lukasznowarkiewicz/ApplianceConnector/imagesAndVideos/api_sample.png

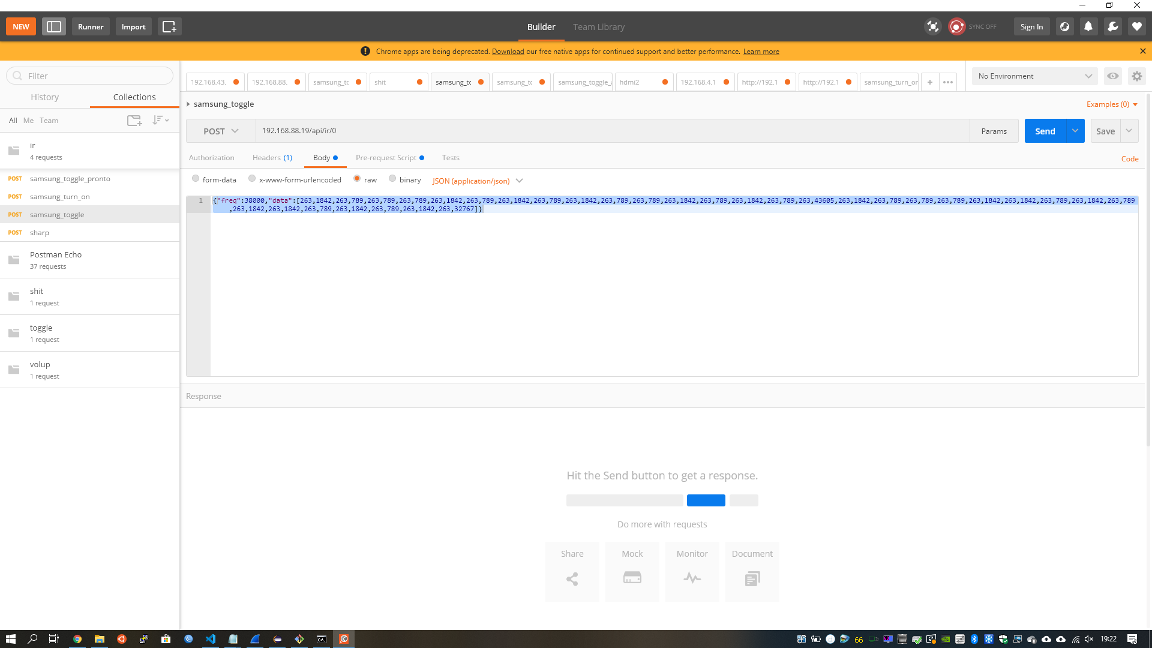
imagesAndVideos/api_sample.png
