lukasznowarkiewicz/ApplianceConnector/imagesAndVideos/box2.png

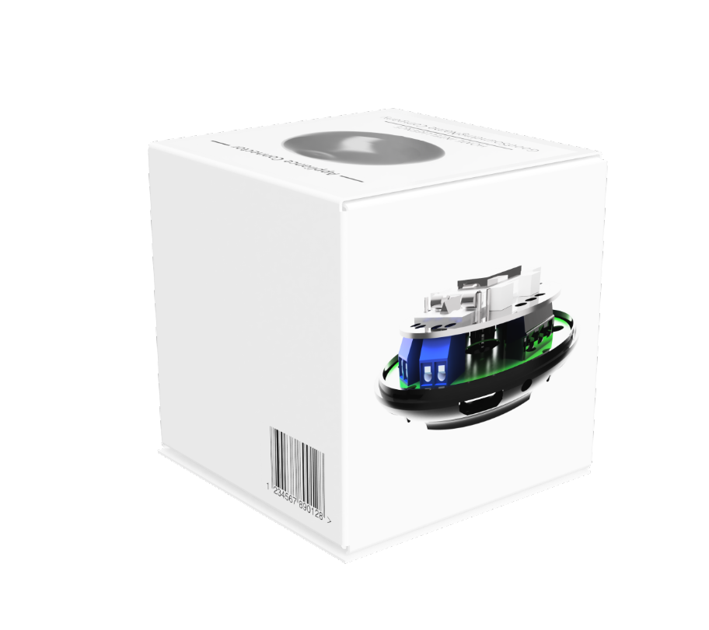
imagesAndVideos/box2.png
