lukasznowarkiewicz/ApplianceConnector/imagesAndVideos/box.png

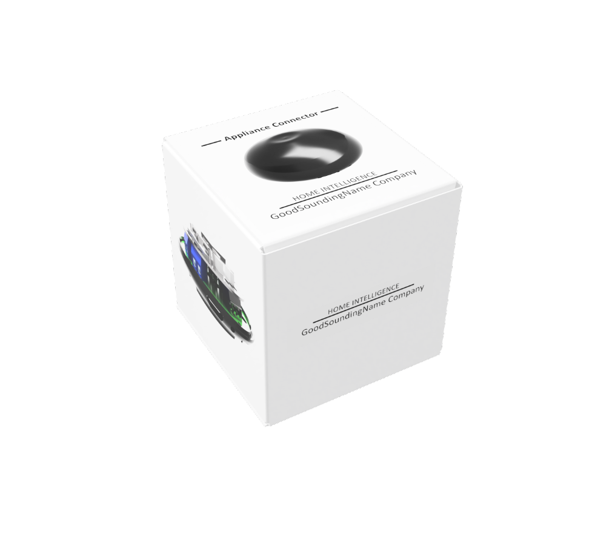
imagesAndVideos/box.png
