lukasznowarkiewicz/ApplianceConnector/imagesAndVideos/casing/casing_bottom_view.jpeg

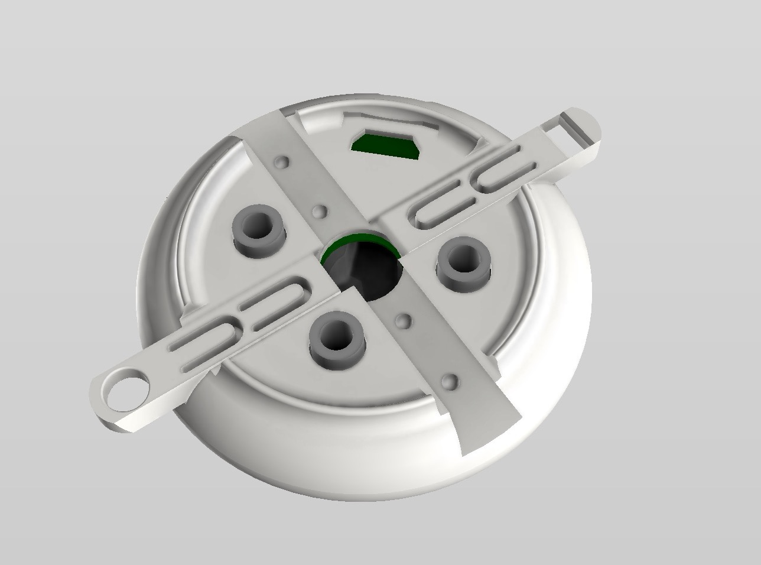
imagesAndVideos/casing/casing_bottom_view.jpeg
