lukasznowarkiewicz/ApplianceConnector/imagesAndVideos/casing/casing_render.jpg

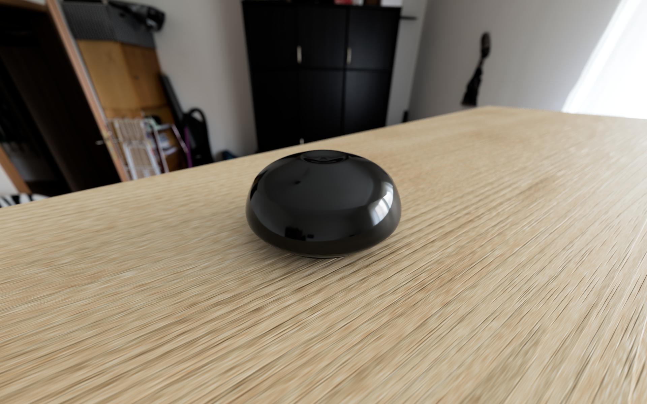
imagesAndVideos/casing/casing_render.jpg
