lukasznowarkiewicz/ApplianceConnector/imagesAndVideos/devKit_prepapration.jpeg

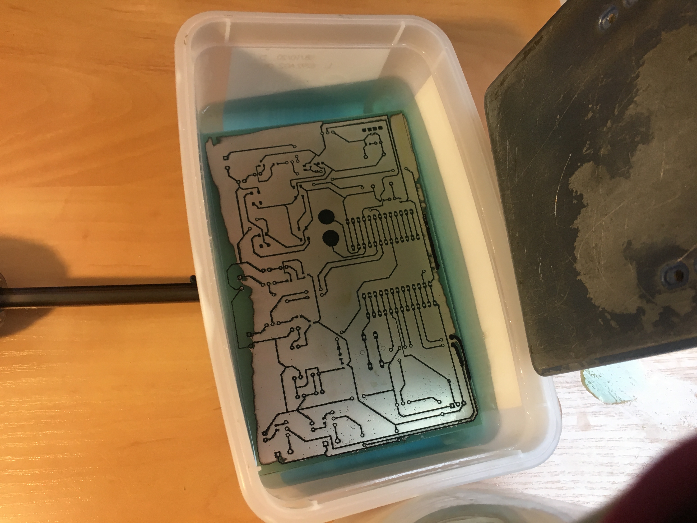
imagesAndVideos/devKit_prepapration.jpeg
