lukasznowarkiewicz/ApplianceConnector/imagesAndVideos/software/authentication.png

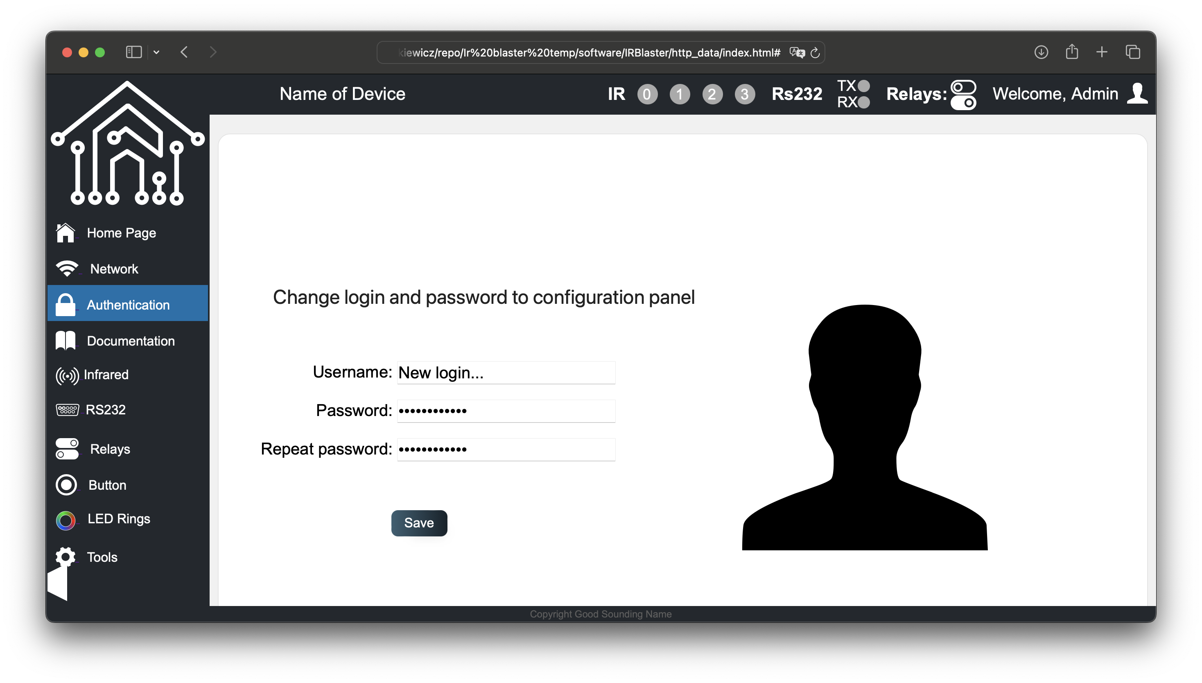
imagesAndVideos/software/authentication.png
