lukasznowarkiewicz/ApplianceConnector/imagesAndVideos/software/button1.png

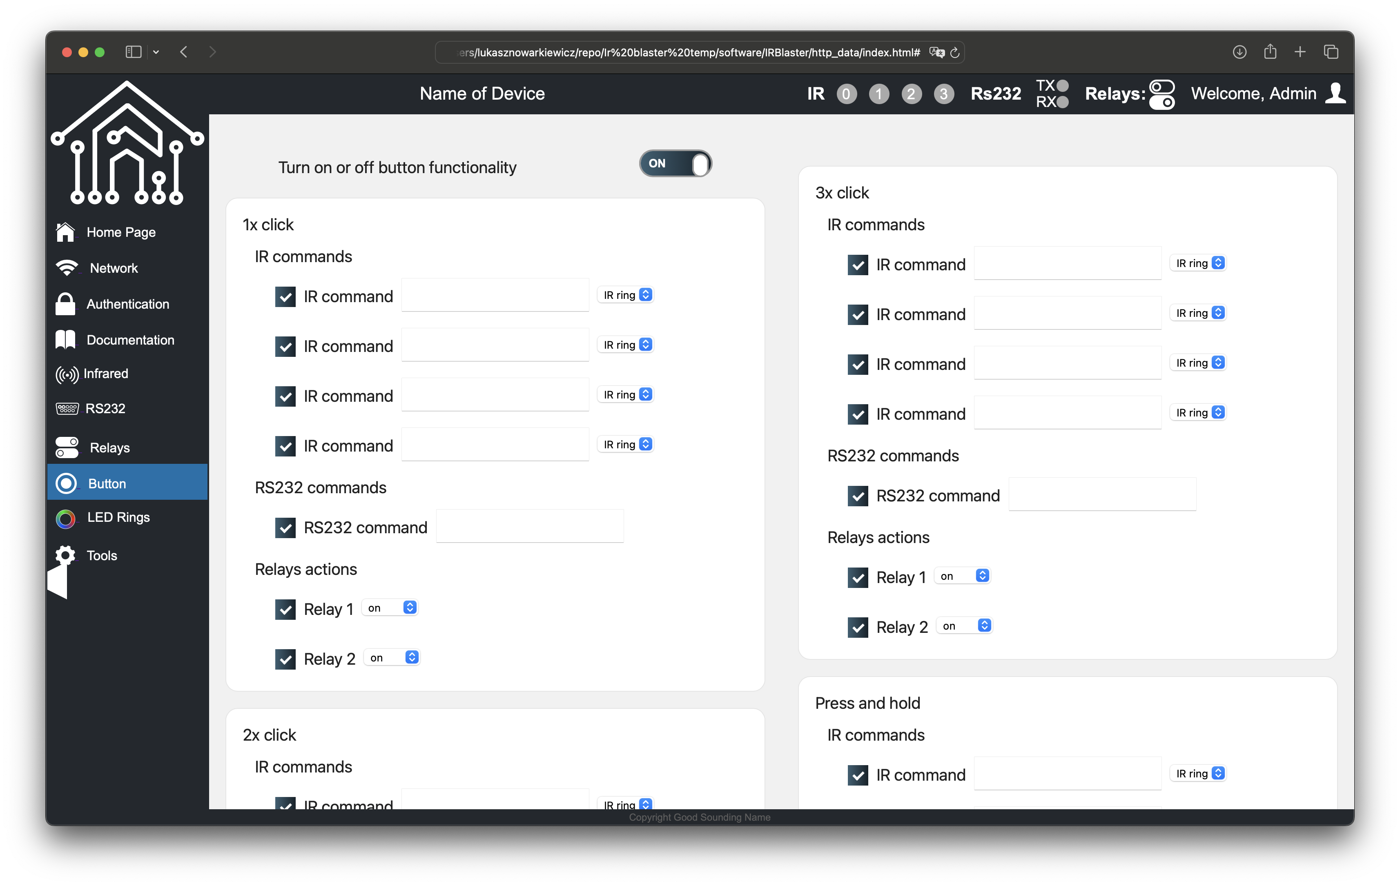
imagesAndVideos/software/button1.png
