lukasznowarkiewicz/ApplianceConnector/imagesAndVideos/software/button2.png

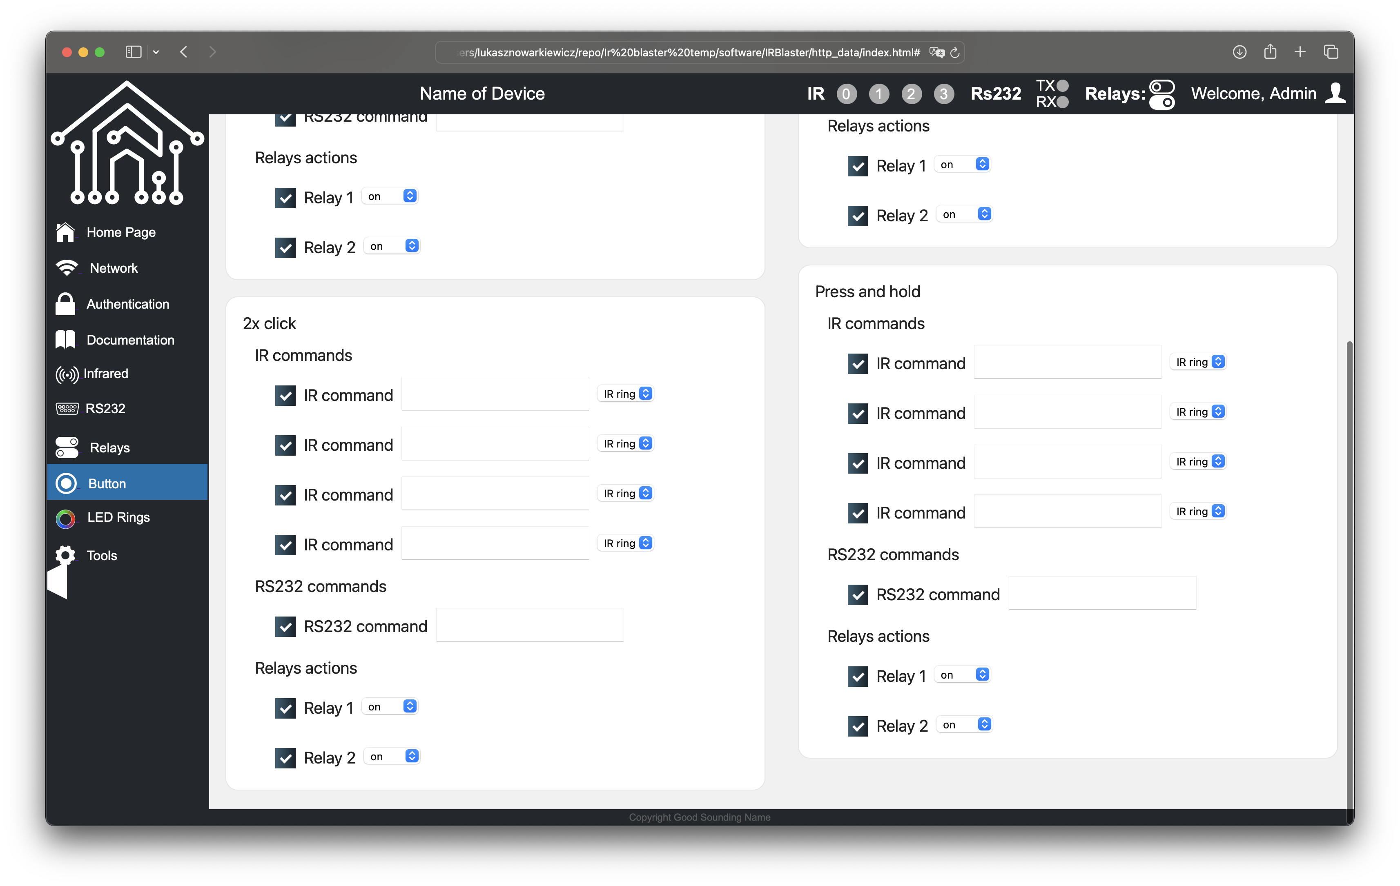
imagesAndVideos/software/button2.png
