lukasznowarkiewicz/ApplianceConnector/imagesAndVideos/software/documentation.png

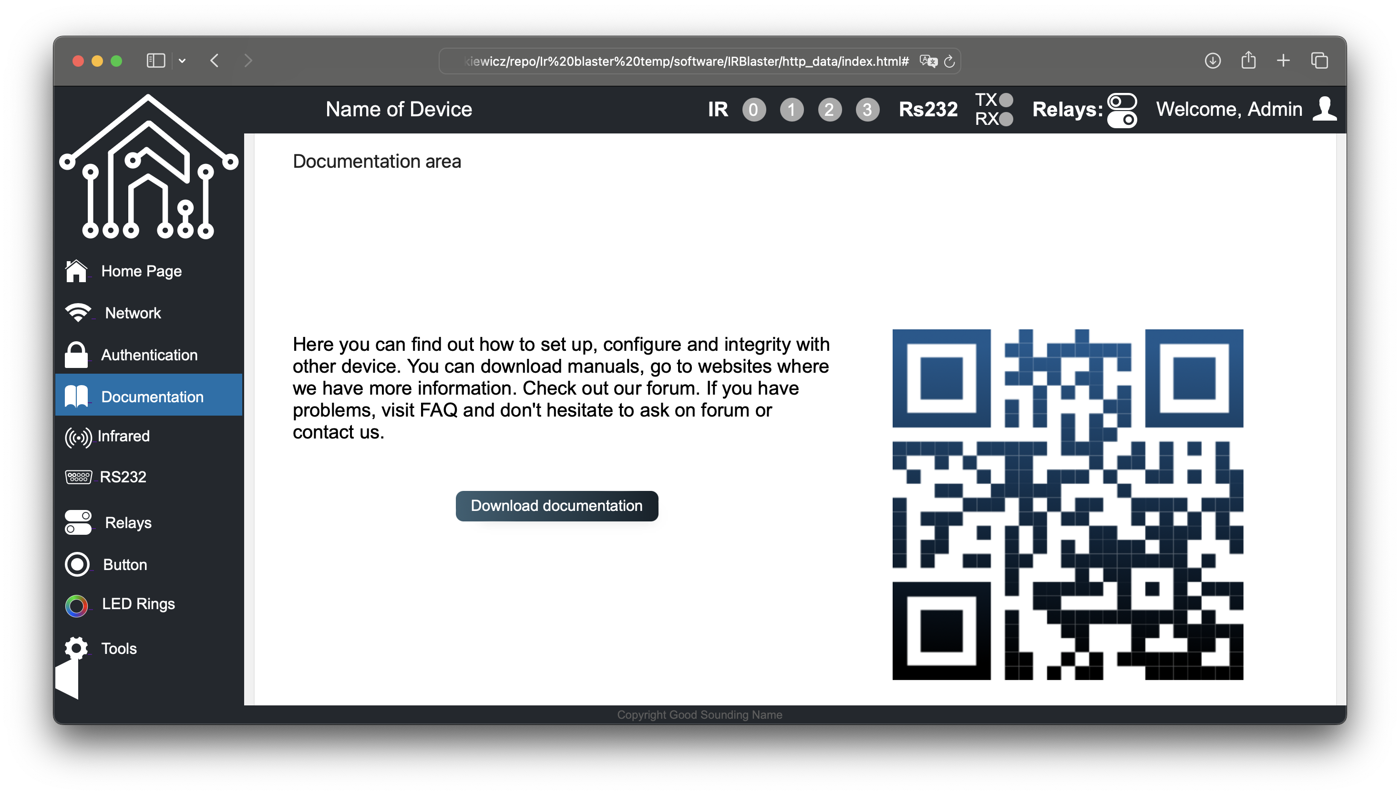
imagesAndVideos/software/documentation.png
