lukasznowarkiewicz/ApplianceConnector/imagesAndVideos/software/homePages.png

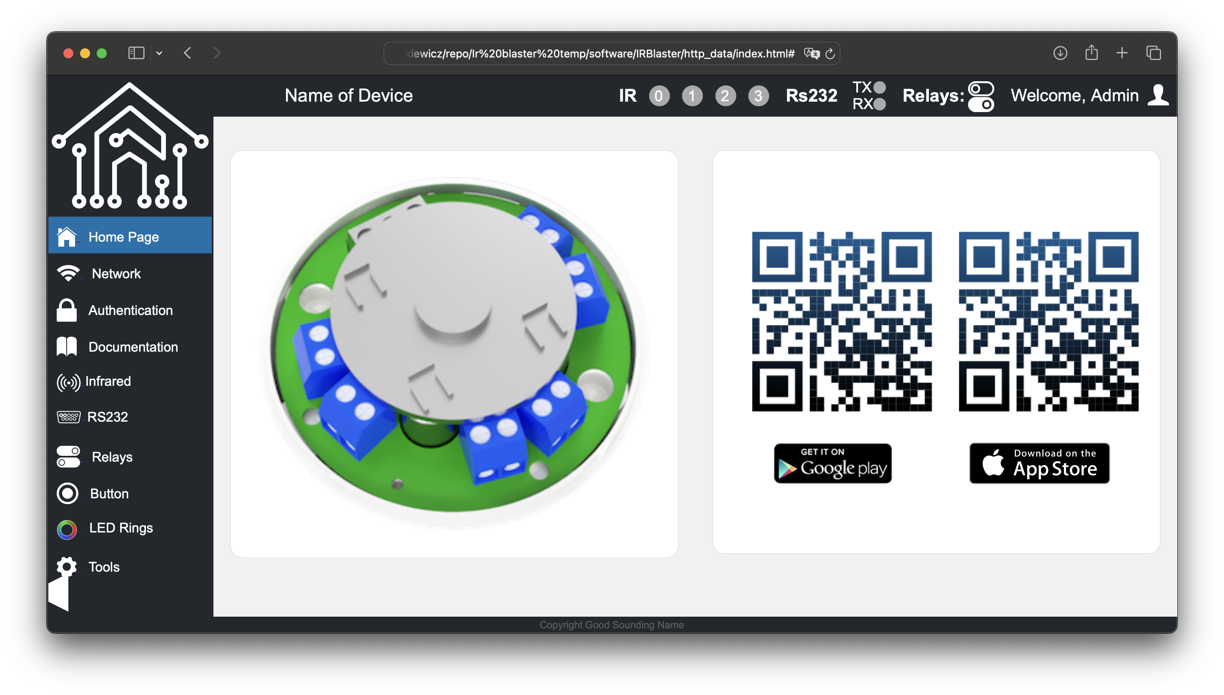
imagesAndVideos/software/homePages.png
