lukasznowarkiewicz/ApplianceConnector/imagesAndVideos/software/infrared.png

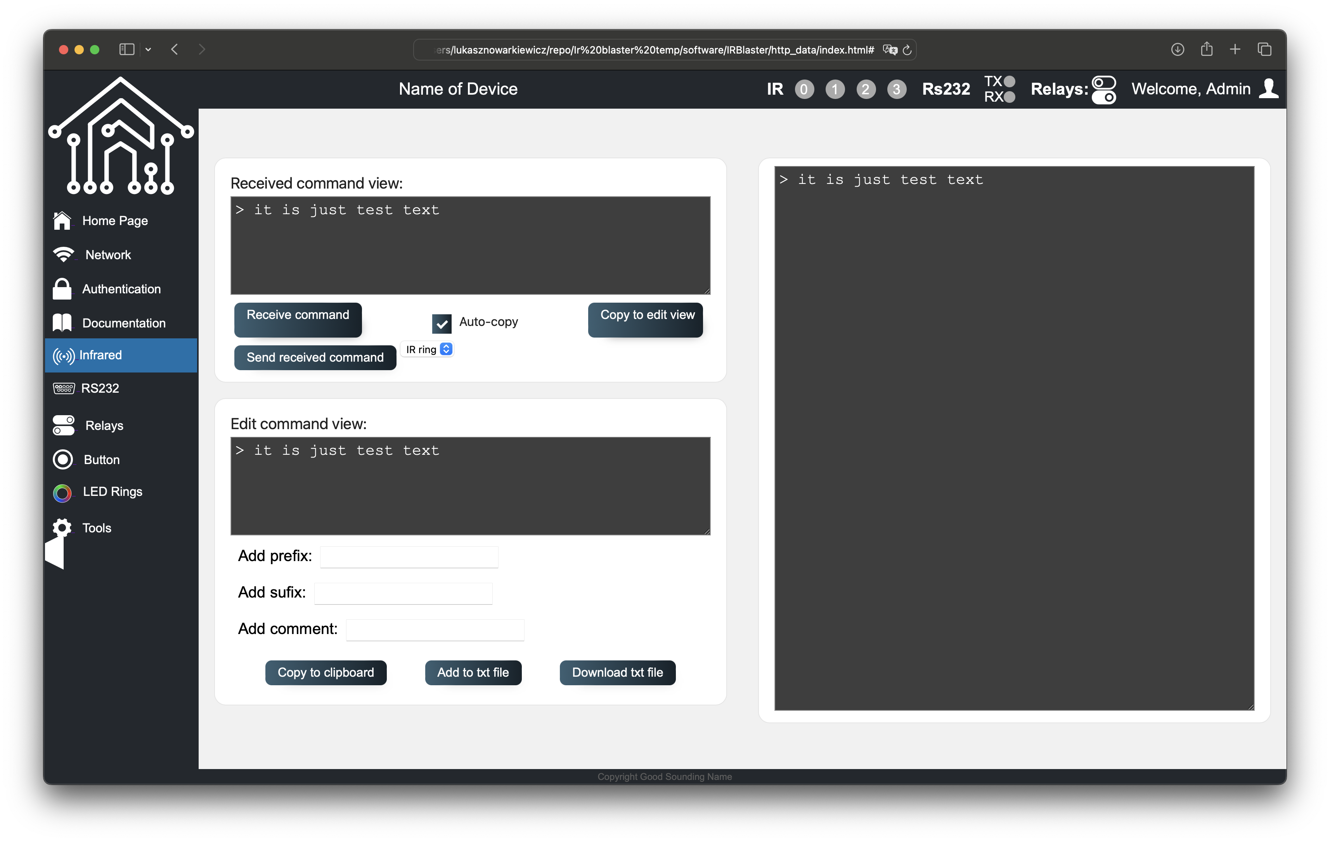
imagesAndVideos/software/infrared.png
