lukasznowarkiewicz/ApplianceConnector/imagesAndVideos/software/ledRing.png

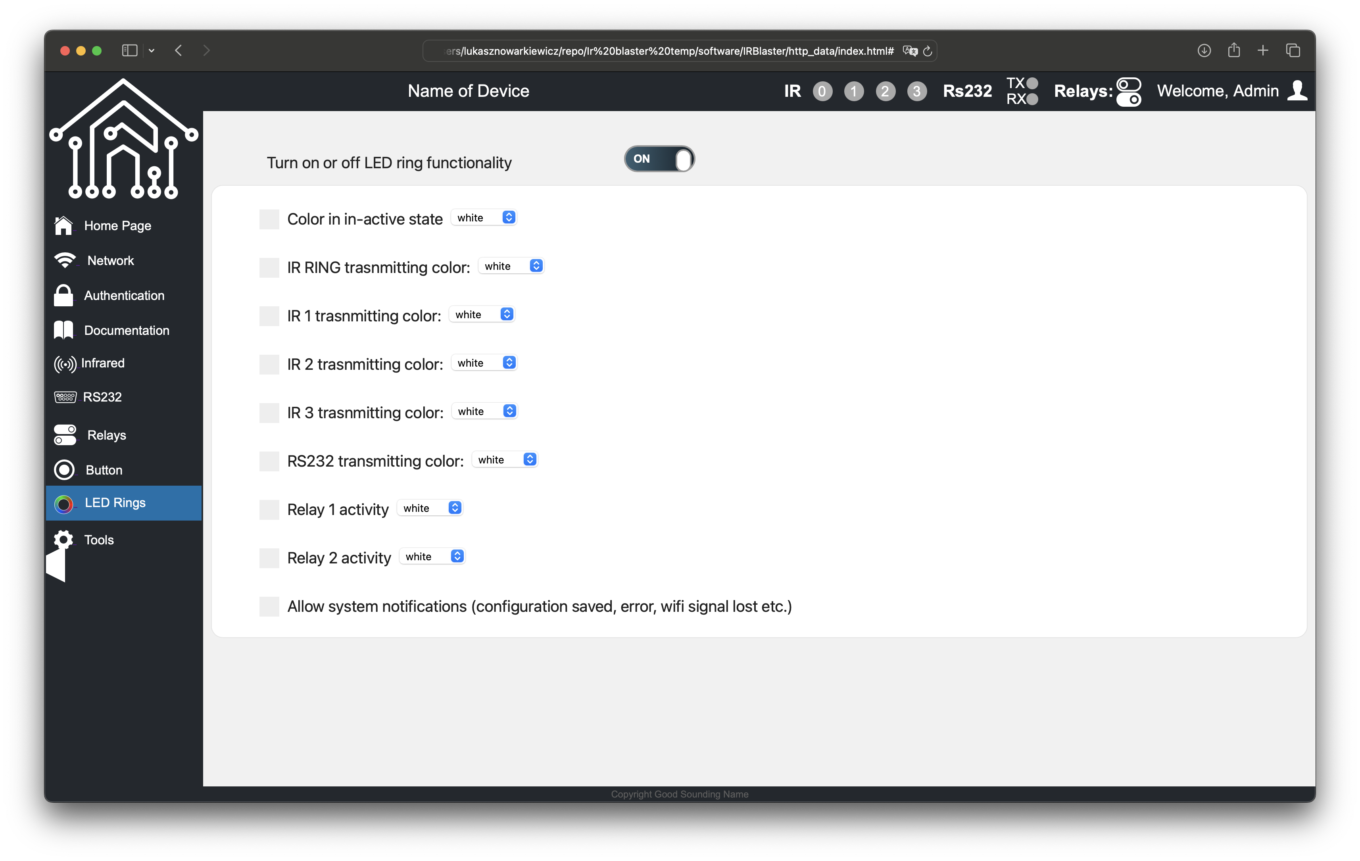
imagesAndVideos/software/ledRing.png
