lukasznowarkiewicz/ApplianceConnector/imagesAndVideos/software/network.png

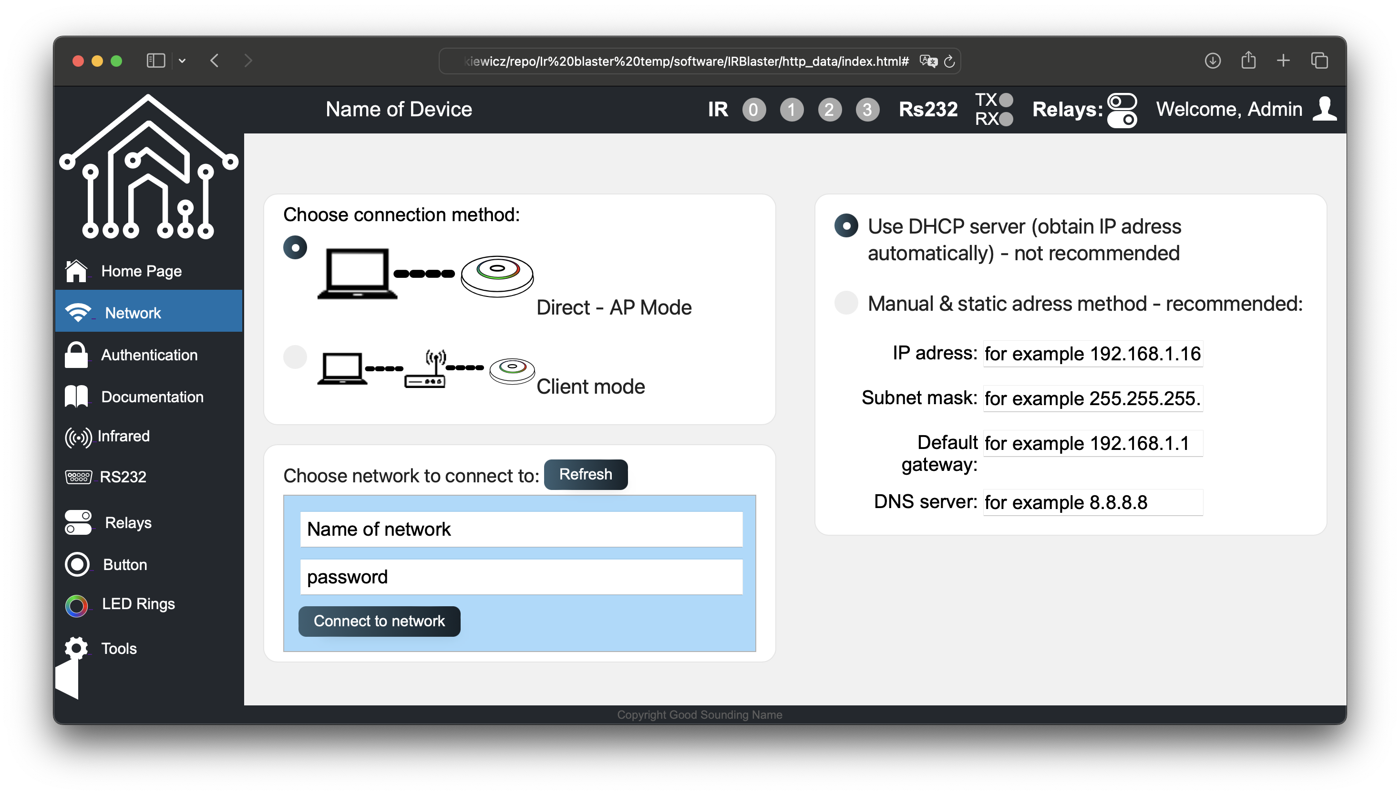
imagesAndVideos/software/network.png
