lukasznowarkiewicz/ApplianceConnector/imagesAndVideos/software/relays.png

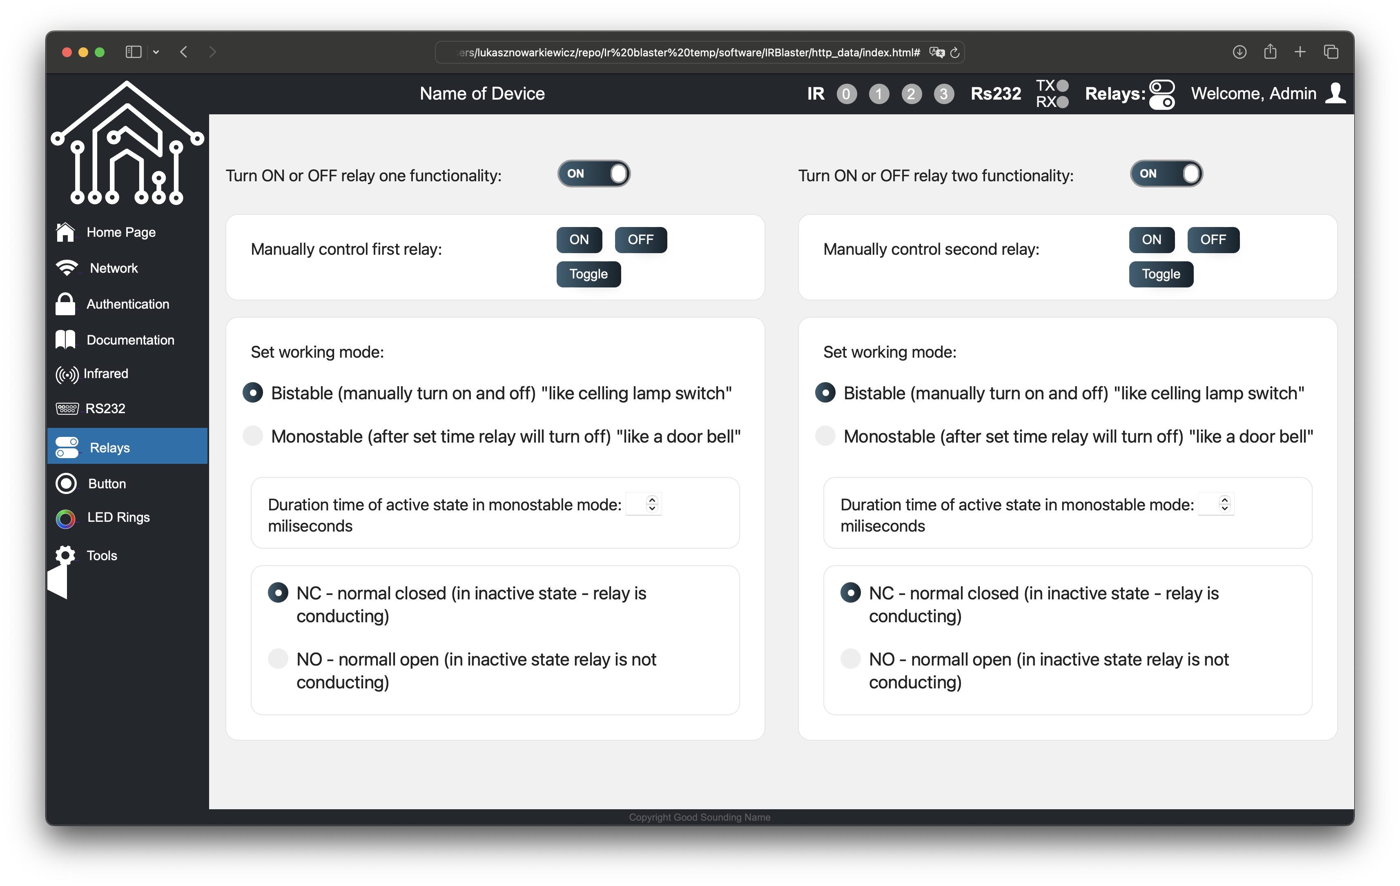
imagesAndVideos/software/relays.png
