lukasznowarkiewicz/ApplianceConnector/imagesAndVideos/software/rs232.png

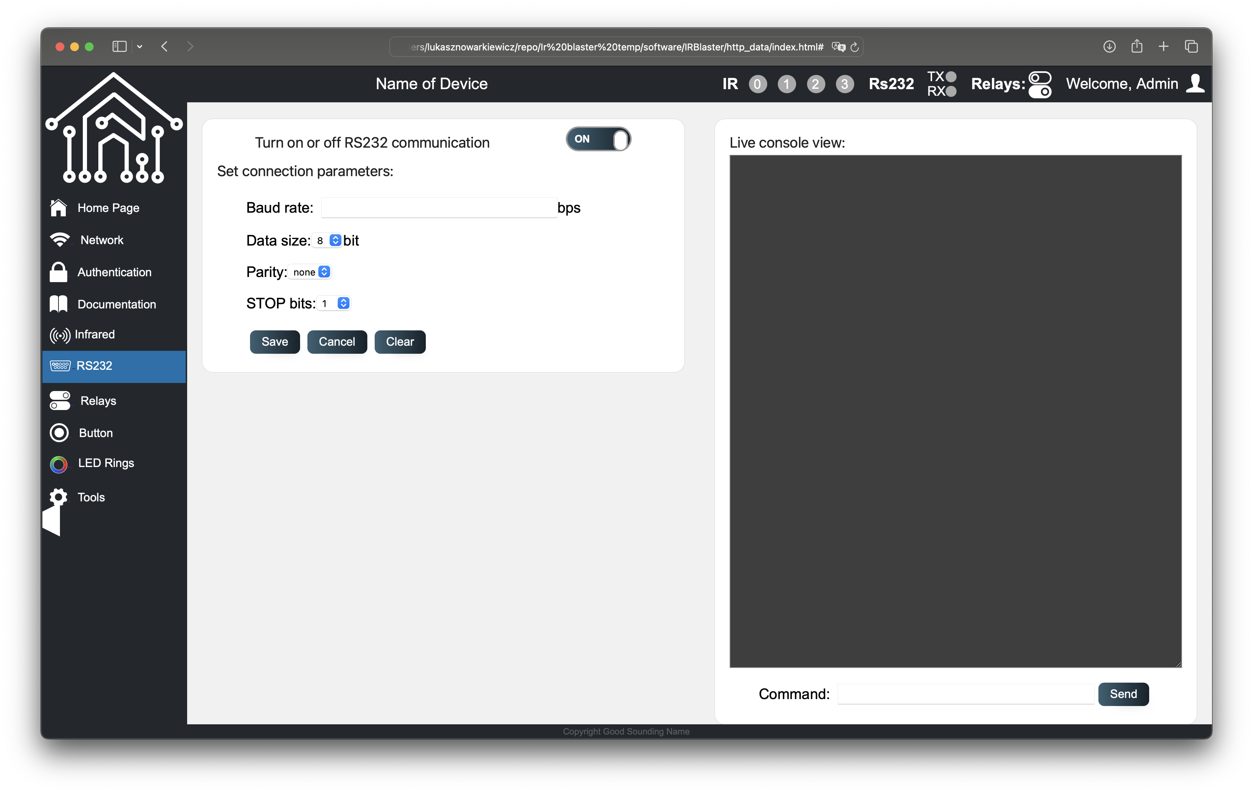
imagesAndVideos/software/rs232.png
