lukasznowarkiewicz/ApplianceConnector/imagesAndVideos/software/tools.png

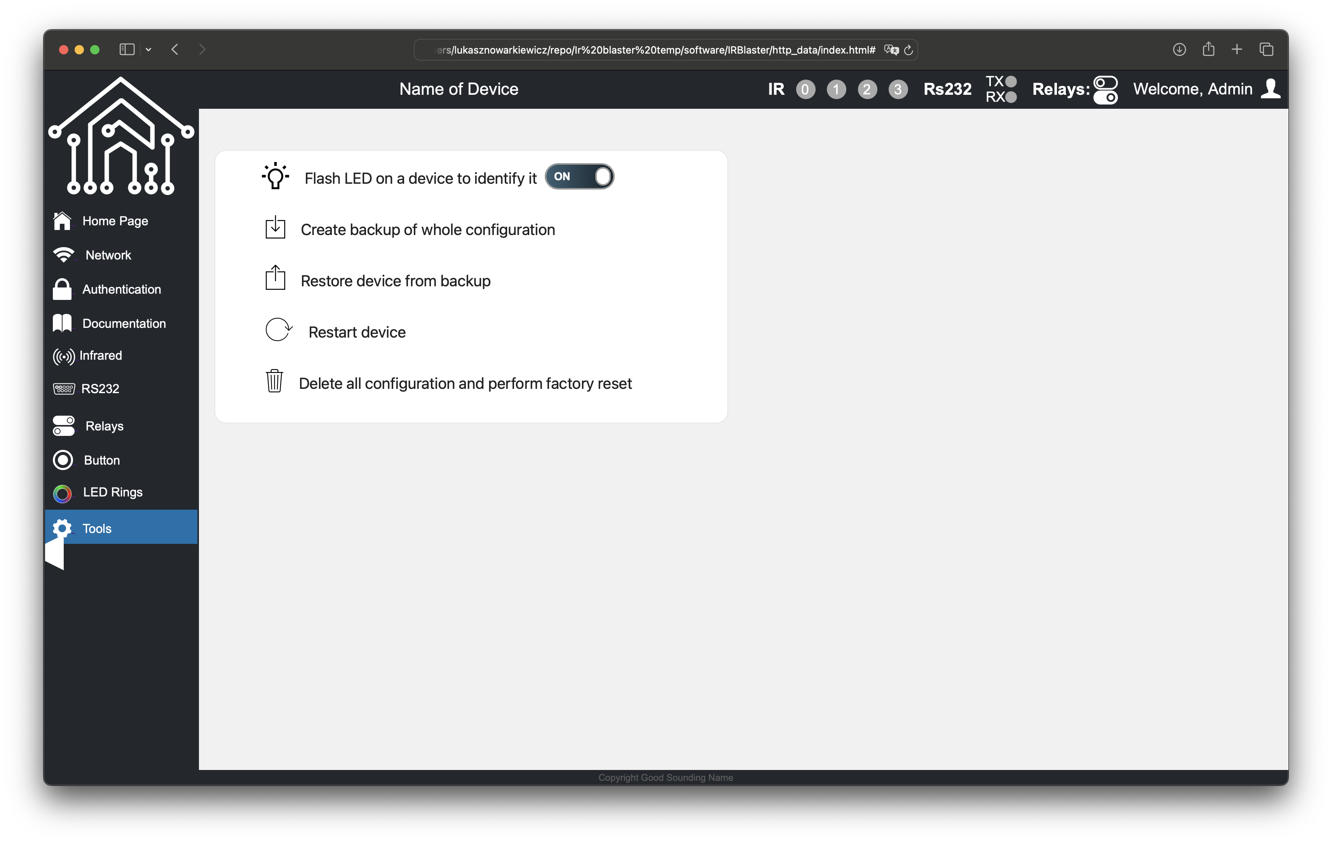
imagesAndVideos/software/tools.png
