lukasznowarkiewicz/ApplianceConnector/imagesAndVideos/UI_creation_based_on_project.png

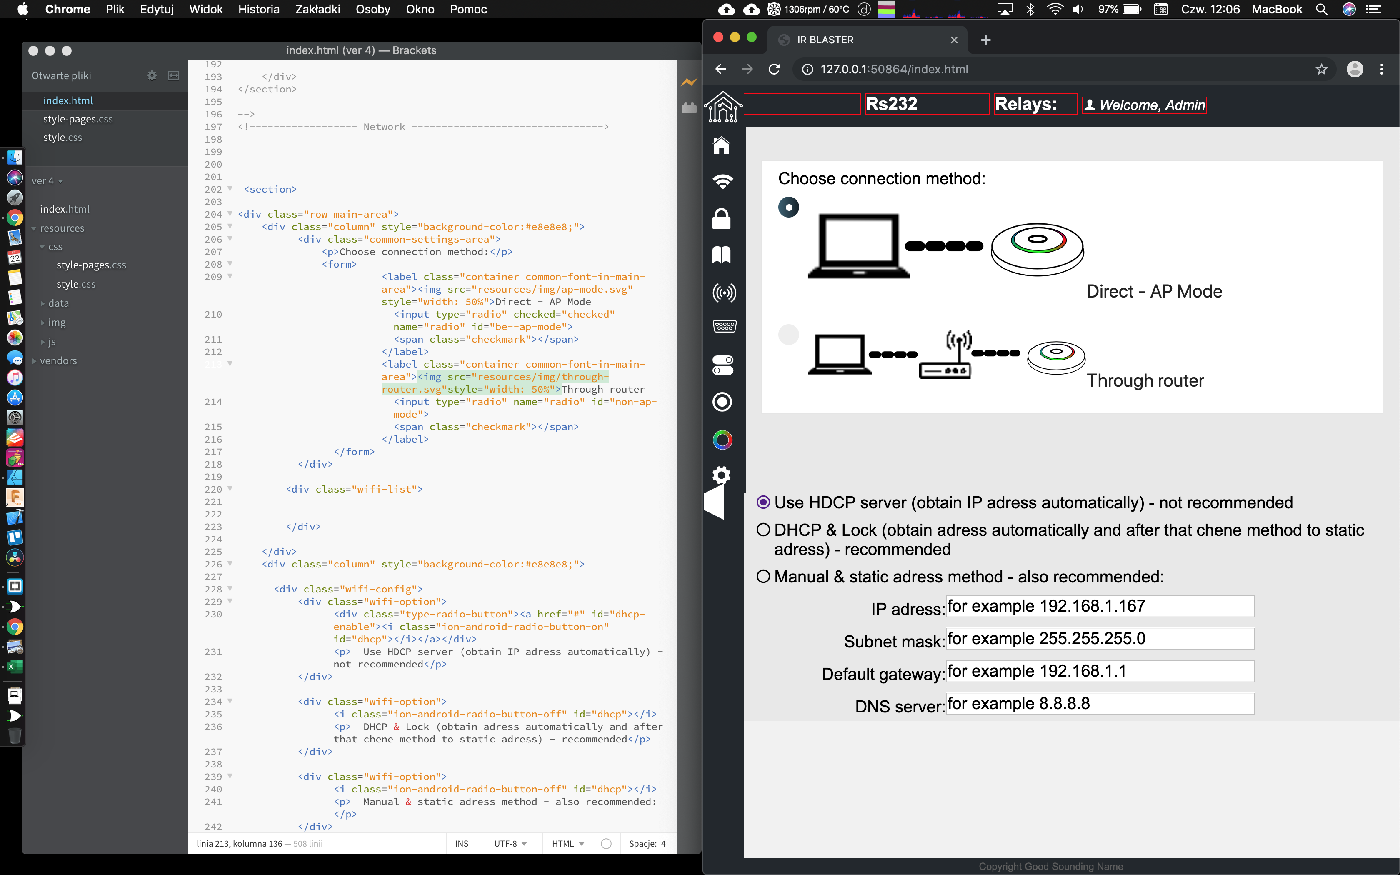
imagesAndVideos/UI_creation_based_on_project.png
