lukasznowarkiewicz/ApplianceConnector/UIDesign/Button.jpg

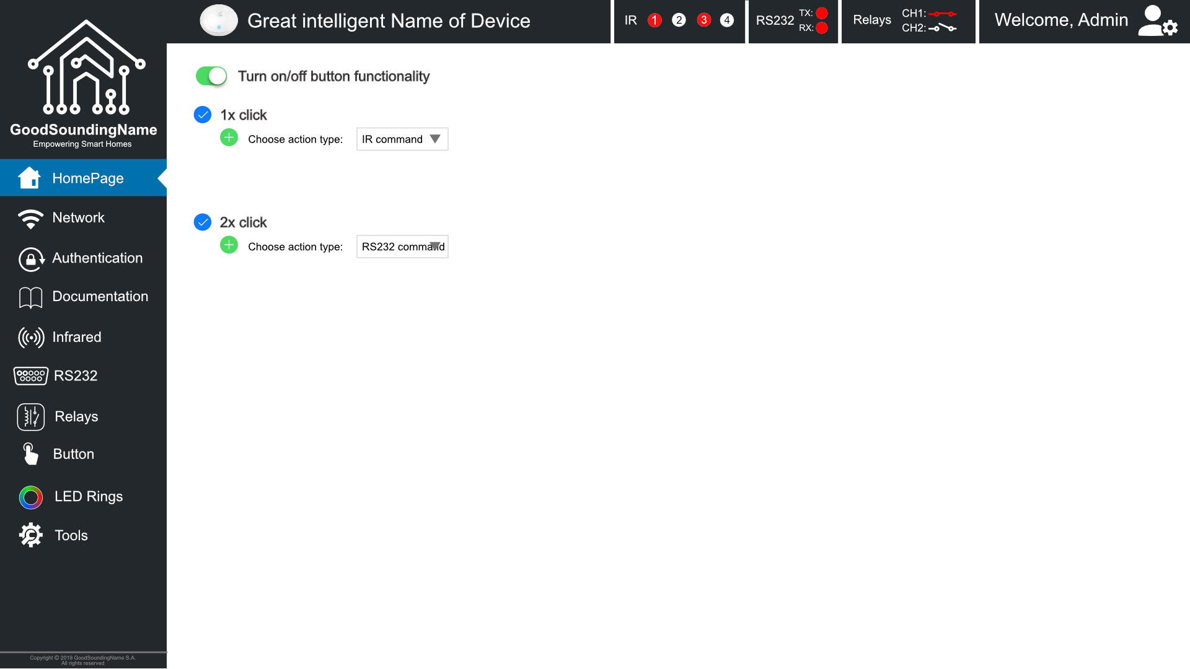
UIDesign/Button.jpg
