lukasznowarkiewicz/ApplianceConnector/UIDesign/LED Rings.jpg

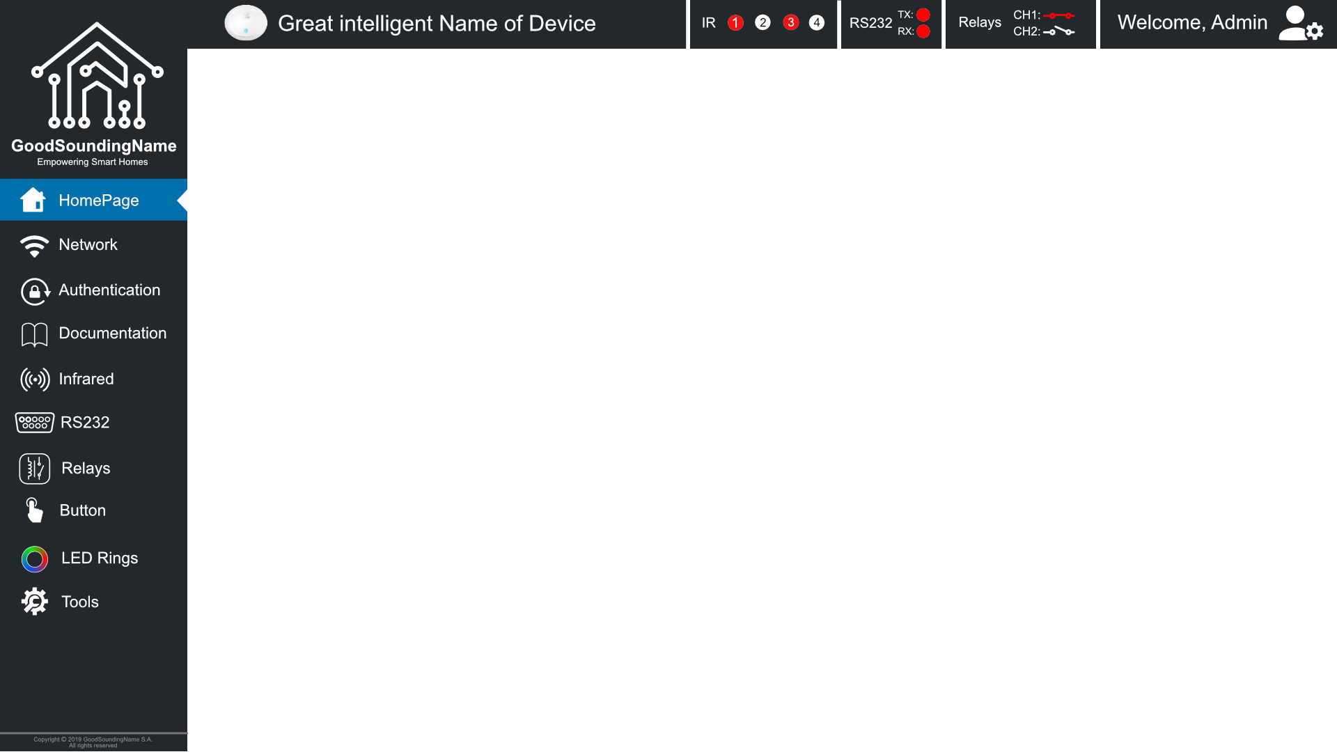
UIDesign/LED Rings.jpg
