lukasznowarkiewicz/ApplianceConnector/UIDesign/Tools.jpg

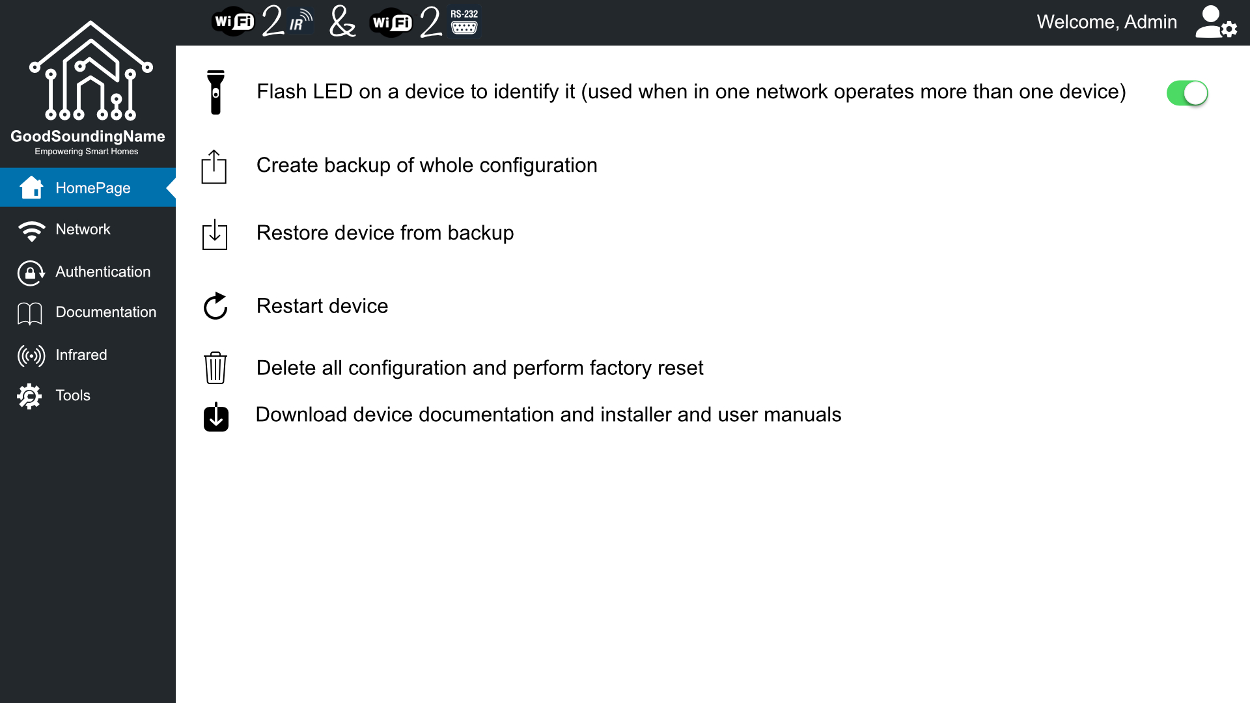
UIDesign/Tools.jpg
