lukasznowarkiewicz/ApplianceConnector/imagesAndVideos/testin_connection_to_wifi.png

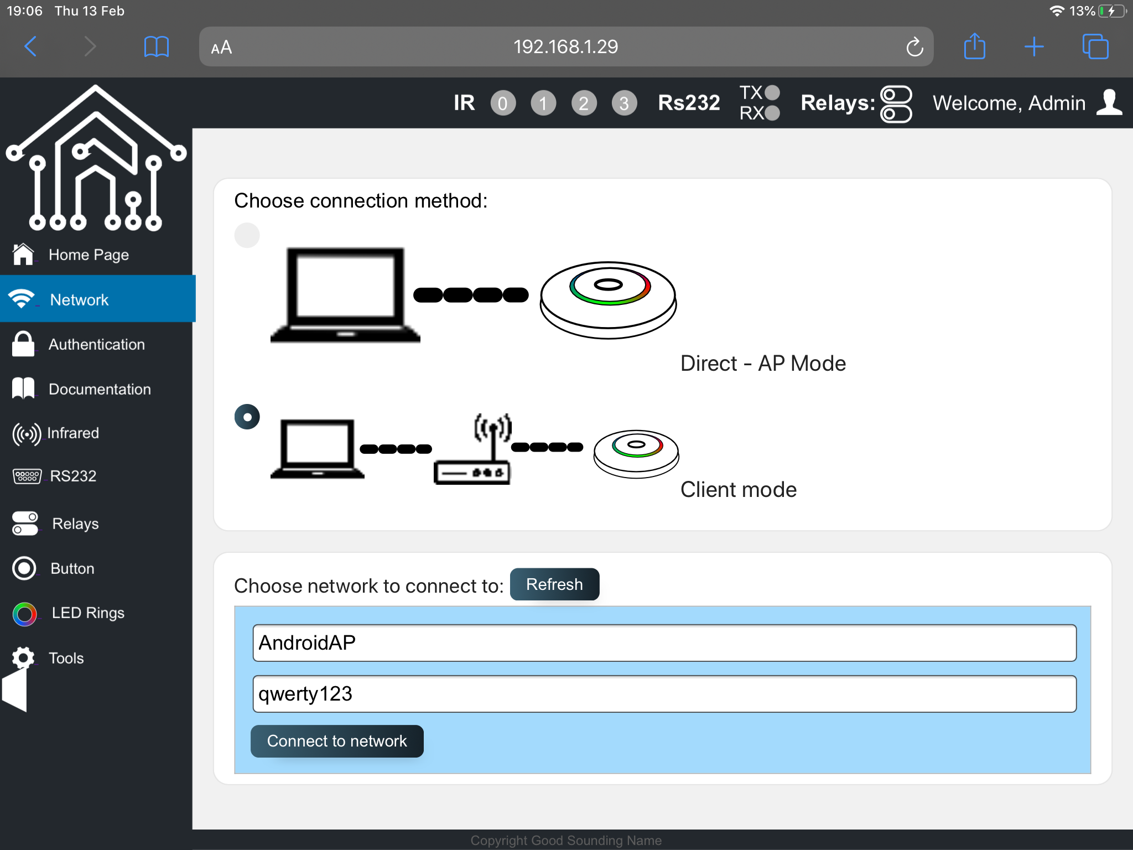
imagesAndVideos/testin_connection_to_wifi.png
